blascarr/DomoLamp/src/DomoLamp_bb.png

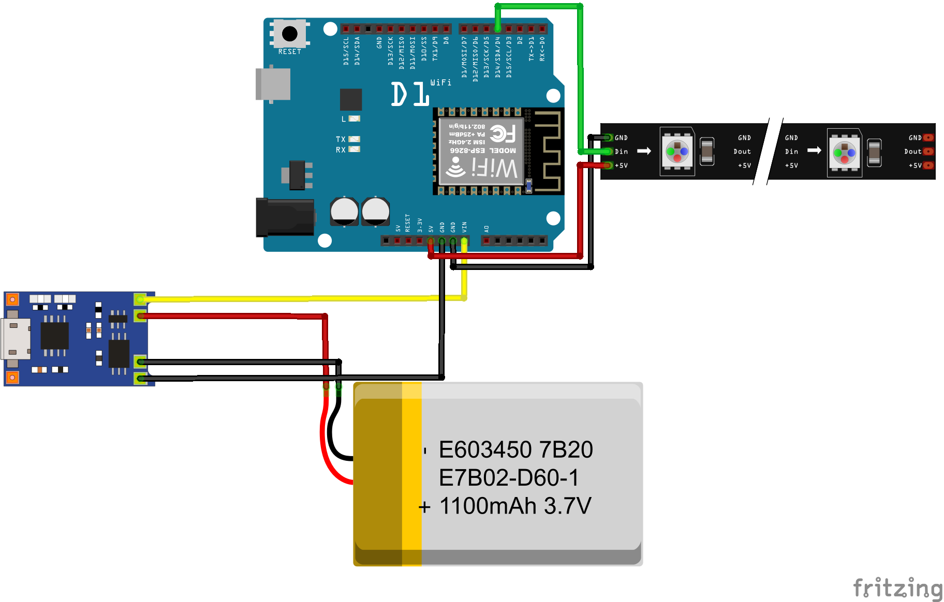
src/DomoLamp_bb.png
